jrhahn/rs-birdscale/src/platform.rs

//! Concrete ESP32-C3 wiring for the sensor abstraction (#12).
//!
//! `sensors/` is HAL-agnostic; this module is where it meets the board. It
//! brings up the buses this node actually needs (per [`node::active`]),
//! constructs the enabled drivers, and offers one `measure_all()` that the
//! publish path can call without knowing what is populated.
//!
//! ## Pin map (Seeed XIAO ESP32-C3 silkscreen -> GPIO)
//!
//! | Pad | GPIO | Use |
//! | --- | --- | --- |
//! | D0 | 2  | HX711 SCK |
//! | D1 | 3  | HX711 DT |
//! | D2 | 4  | DS18B20 1-Wire, *or* the battery divider's tap on ADC1 |
//! | D3 | 5  | SDS011 UART RX (sensor TX) |
//! | D4 | 6  | I²C SDA (SHT31-D, SCD41) |
//! | D5 | 7  | I²C SCL |
//! | D10| 10 | SDS011 UART TX (sensor RX) |
//!
//! The SDS011 deliberately avoids D6/D7 (GPIO21/20): those are the console UART
//! pads, and the log output shares them.
//!
//! The two I²C sensors sit on one bus at different addresses (0x44 / 0x62), so
//! the bus is wrapped in a [`SharedI2c`] handle that each driver can own.

use embassy_sync::{blocking_mutex::raw::NoopRawMutex, mutex::Mutex};
use embassy_time::{with_timeout, Duration, TimeoutError};
use embedded_hal_async::i2c::{ErrorType, I2c as I2cTrait, Operation};
use esp_hal::{
    gpio::GpioPin,
    i2c::master::{Config as I2cConfig, Error as I2cError, I2c},
    peripherals::{I2C0, UART1},
    uart::{Config as UartConfig, Uart},
    Async,
};
use heapless::Vec;
use log::{info, warn};
use static_cell::StaticCell;

use crate::node::{self, Slot};
use crate::sensors::{
    scd41, scd41::Scd41, sds011::Sds011, sgp41, sgp41::Sgp41, sht31, sht31::Sht31, Reading, Sensor,
};

/// SDS011 baud rate (fixed in hardware).
const SDS011_BAUD: u32 = 9600;

/// Upper bound on the readings one round can produce: weight + probe
/// temperature + SHT31 (2) + SCD41 (3) + SDS011 (2) + cell voltage + link
/// RSSI, with headroom.
///
/// Kept in step with [`crate::discovery::MAX_ENTITIES`]: a node that announces
/// an entity it then has no room to report would look broken in exactly the
/// way that is hardest to see, because `push_sample` drops silently.
pub const MAX_SAMPLES: usize = 14;

/// One reading plus the node-level key prefix that disambiguates it (see
/// [`Slot`]). The publish path turns this into `<ns>/<node>/<prefix><key>`.
pub struct Sample {
    pub prefix: &'static str,
    pub reading: Reading,
}

/// The set of readings gathered in one round.
pub type Samples = Vec<Sample, MAX_SAMPLES>;

// --- Shared I²C bus ----------------------------------------------------------

type I2cBus = I2c<'static, Async>;
static I2C_BUS: StaticCell<Mutex<NoopRawMutex, I2cBus>> = StaticCell::new();

/// A cloneable handle to the one I²C peripheral, so both I²C drivers can own
/// their bus (as the [`Sensor`] contract wants) while sharing the hardware.
/// `NoopRawMutex` is sufficient: everything runs on the single-core executor and
/// measurements are sequential, the lock only enforces that at compile time.
#[derive(Clone, Copy)]
pub struct SharedI2c(&'static Mutex<NoopRawMutex, I2cBus>);

impl ErrorType for SharedI2c {
    type Error = I2cError;
}

/// Ceiling on one I²C transaction. Nothing on this bus is slow: the longest
/// thing any driver asks for is a handful of bytes at 100 kHz, and the sensors'
/// own conversion waits happen *between* transactions, not inside them. So a
/// transaction still running after this is not slow, it is stuck.
///
/// It exists because the alternative is worse than an error. `transaction` is
/// awaited with no bound of its own, so a bus wedged by a device holding SDA
/// low parks the caller for ever: no reading, no log line, and eventually the
/// system watchdog reboots the node — which is what `rst:0x7 (TG0WDT_SYS_RST)`
/// in the outdoor node's log was. A timeout turns that into a failed reading
/// the drivers already know how to report.
pub const I2C_TIMEOUT_MS: u64 = 100;

impl I2cTrait for SharedI2c {
    async fn transaction(
        &mut self,
        address: u8,
        operations: &mut [Operation<'_>],
    ) -> Result<(), Self::Error> {
        // Spell the trait out: esp-hal's `I2c` also has an inherent
        // `transaction` taking its own `Operation` type, which would shadow this.
        let mut bus = self.0.lock().await;
        match with_timeout(
            Duration::from_millis(I2C_TIMEOUT_MS),
            I2cTrait::transaction(&mut *bus, address, operations),
        )
        .await
        {
            Ok(result) => result,
            Err(TimeoutError) => {
                warn!(
                    "I²C transaction to 0x{address:02X} timed out after {I2C_TIMEOUT_MS} ms;                      treating it as a bus fault rather than waiting for the watchdog"
                );
                Err(I2cError::TimeOut)
            }
        }
    }
}

// --- Peripherals this module may claim ---------------------------------------

/// The peripherals the sensor platform can take over. `main` hands these across
/// wholesale; which of them are actually touched depends on the identity.
pub struct Peripherals {
    pub i2c0: I2C0,
    pub sda: GpioPin<6>,
    pub scl: GpioPin<7>,
    pub uart1: UART1,
    pub uart_rx: GpioPin<5>,
    pub uart_tx: GpioPin<10>,
}

/// The drivers populated on this node. Absent sensors are simply `None`, so the
/// publish path is the same code for every node in the fleet.
pub struct Sensors {
    bus: Option<SharedI2c>,
    sht31: Option<Sht31<SharedI2c>>,
    scd41: Option<Scd41<SharedI2c>>,
    sds011: Option<Sds011<Uart<'static, Async>>>,
    /// Unlike every other driver here this one is not read once a round:
    /// its hotplate only stays comparable while it is sampled at 1 Hz, so
    /// [`Sensors::step_gas`] drives it between rounds and `measure_all`
    /// merely collects whatever index those steps produced.
    sgp41: Option<Sgp41<SharedI2c>>,
    /// Whether the I²C bring-up probe has already run this boot.
    probed: bool,
    /// Consecutive rounds the SCD41 produced nothing, and whether its self test
    /// has already run for this streak (see [`SCD41_SELF_TEST_AFTER`]).
    scd41_empty_rounds: u8,
    scd41_self_tested: bool,
    /// Base rounds elapsed since boot, so a slot with its own slower cadence
    /// knows which of them are its own (see [`Slot::rounds_between`]).
    round: u32,
    /// κ in hundredths, from the live config, handed to the SDS011 with the
    /// humidity just before it measures.
    kappa_centi: u32,
}

/// Empty SCD41 rounds before the driver asks the sensor to test itself.
///
/// Three, because one empty round is normal — periodic mode reports nothing
/// until the first conversion finishes — and two in a row can still be a
/// restart. Three is a fault worth ten seconds of diagnosis.
const SCD41_SELF_TEST_AFTER: u8 = 3;

impl Sensors {
    /// Bring up only the buses this node needs and construct its drivers.
    /// [`node::init`] must have run first — the identity decides what exists.
    pub fn new(p: Peripherals) -> Self {
        let node = node::active();

        let bus = if node.uses_i2c() {
            let i2c = I2c::new(p.i2c0, I2cConfig::default())
                .with_sda(p.sda)
                .with_scl(p.scl)
                .into_async();
            Some(SharedI2c(I2C_BUS.init(Mutex::new(i2c))))
        } else {
            None
        };

        let sht31 = match (bus, node.sht31.enabled) {
            (Some(bus), true) => Some(Sht31::new(bus)),
            _ => None,
        };
        let scd41 = match (bus, node.scd41.enabled) {
            (Some(bus), true) => Some(Scd41::new(bus, node.scd41_mode())),
            _ => None,
        };
        let sgp41 = match (bus, node.sgp41.enabled) {
            (Some(bus), true) => Some(Sgp41::new(bus)),
            _ => None,
        };

        let sds011 = if node.uses_uart() {
            // A UART that fails to configure is a wiring/build mistake, not a
            // runtime condition, so log it and carry on without the sensor.
            match Uart::new_with_config(
                p.uart1,
                UartConfig::default().baudrate(SDS011_BAUD),
                p.uart_rx,
                p.uart_tx,
            ) {
                Ok(uart) => {
                    Some(Sds011::new(uart.into_async()).compensated(node.sds011.compensated))
                }
                Err(e) => {
                    warn!("SDS011 UART init failed: {:?}; sensor disabled", e);
                    None
                }
            }
        } else {
            None
        };

        Self {
            bus,
            sht31,
            scd41,
            sds011,
            sgp41,
            probed: false,
            scd41_empty_rounds: 0,
            scd41_self_tested: false,
            round: 0,
            kappa_centi: crate::sensors::sds011::KAPPA_CENTI_DEFAULT,
        }
    }

    /// Hand the SCD41 its temperature offset (hundredths of °C) from the live
    /// config. A no-op on a node without one, and cheap enough to call every
    /// round — the driver only touches the bus when the value actually changed.
    pub fn set_scd41_offset(&mut self, centi: i32) {
        if let Some(scd41) = self.scd41.as_mut() {
            scd41.set_temperature_offset(centi);
        }
    }

    /// Hand the SDS011 its humidity-correction constant from the live config.
    /// A no-op on a node without one; the humidity itself is picked up inside
    /// [`Sensors::measure_all`], where the SHT31 has just been read.
    pub fn set_sds011_kappa(&mut self, centi: u32) {
        self.kappa_centi = centi;
    }

    /// One 1 Hz step of the gas sensor. A no-op on a node without one.
    ///
    /// This exists because the SGP4x is the one part here that cannot be read
    /// once a round: what it returns is a hotplate resistance, comparable only
    /// while the heater keeps running, and Sensirion's index algorithm is
    /// specified for a 0.5-10 s interval. Sampled once a minute it would yield
    /// a number that looks like a VOC index and is not one -- so the caller
    /// ticks this every second between publishes and `measure_all` only reports
    /// what the ticks computed.
    pub async fn step_gas(&mut self) {
        if let Some(s) = self.sgp41.as_mut() {
            s.sample_once().await;
        }
    }

    /// Whether this node has a gas sensor at all, so the caller can skip the
    /// 1 Hz loop entirely rather than ticking a `None` once a second.
    pub fn has_gas_sensor(&self) -> bool {
        self.sgp41.is_some()
    }

    /// Ask each expected I²C address whether anything is there, and say so in
    /// the log. Without this a wiring fault, a missing pull-up and a strapped
    /// address all look identical from the outside: "not responding".
    ///
    /// The probe commands are side-effect-free reads, and an SHT31-D found only
    /// at the alternate address is adopted rather than reported as missing —
    /// breakouts differ on how they strap ADDR.
    async fn probe_i2c(&mut self) {
        let Some(bus) = self.bus else { return };
        let mut missing = false;

        if self.sht31.is_some() {
            // Ask for a known state before asking anything else. A battery node
            // cold-boots every couple of seconds while the sensor stays powered
            // from 3V3, so a restart can land mid-transaction and leave the
            // SHT31 part-way through a command -- still ACKing its address, so
            // the bus scan finds it, but NAKing what comes next. That is the
            // "0x44 answered" / "no SHT31-D at 0x44" pair in the log.
            if let Some(s) = self.sht31.as_mut() {
                s.soft_reset().await;
            }
            let primary = acks(bus, sht31::ADDR, sht31::CMD_READ_STATUS).await;
            let alt = acks(bus, sht31::ADDR_ALT, sht31::CMD_READ_STATUS).await;
            match (primary, alt) {
                (true, _) => info!("SHT31-D found at 0x{:02X}", sht31::ADDR),
                (false, true) => {
                    info!(
                        "SHT31-D found at 0x{:02X} (ADDR strapped high); using it",
                        sht31::ADDR_ALT
                    );
                    let mut moved = Sht31::with_address(bus, sht31::ADDR_ALT);
                    // The reset above went to the default address, which is not
                    // where this one lives.
                    moved.soft_reset().await;
                    self.sht31 = Some(moved);
                }
                (false, false) => {
                    missing = true;
                    warn!(
                        "no SHT31-D at 0x{:02X} or 0x{:02X}",
                        sht31::ADDR,
                        sht31::ADDR_ALT
                    );
                }
            }
        }

        if self.scd41.is_some() {
            if acks(bus, scd41::ADDR, scd41::CMD_GET_DATA_READY).await {
                info!("SCD41 found at 0x{:02X}", scd41::ADDR);
                // The address ACK only proves something is on the bus. The
                // serial number says *what* — which physical sensor sits in
                // this node, and whether it is plausibly a genuine Sensirion
                // part at all. Counterfeits are common and tend to answer with
                // zeroes or with the same number on every unit.
                if let Some(s) = self.scd41.as_mut() {
                    match s.serial_number().await {
                        Some(0) => warn!(
                            "SCD41 serial number is zero — that is not what a genuine \
                             Sensirion part returns; treat its readings with suspicion"
                        ),
                        Some(serial) => info!("SCD41 serial 0x{:012X}", serial),
                        None => warn!("SCD41 gave no serial number"),
                    }
                }
            } else {
                missing = true;
                warn!("no SCD41 at 0x{:02X}", scd41::ADDR);
            }
        }

        if self.sgp41.is_some() {
            // `detect` is what the sampling path uses anyway, and it answers a
            // question a bare ACK cannot: an SGP40 and an SGP41 share this
            // address, and only one of them has a NOx channel. Breakout
            // listings mix the two up routinely, so the boot log is the place
            // to find out which one is actually fitted.
            if let Some(s) = self.sgp41.as_mut() {
                match s.detect().await {
                    Some(part) => {
                        info!("{:?} found at 0x{:02X}", part, sgp41::ADDR);
                        match s.serial_number().await {
                            Some(serial) => info!("SGP4x serial 0x{:012X}", serial),
                            None => warn!("SGP4x gave no serial number"),
                        }
                    }
                    None => {
                        missing = true;
                        warn!("no SGP4x at 0x{:02X}", sgp41::ADDR);
                    }
                }
            }
        }

        // Only now, and only because something is already wrong: sweep the bus
        // to tell "the bus is dead" from "the bus is fine and the device is
        // somewhere else". Those two look identical from a targeted probe, and
        // they have completely different fixes.
        if missing {
            self.report_scan(bus).await;
        }
    }

    /// Sweep the whole bus and say what that means, in the terms someone
    /// holding a soldering iron can act on.
    async fn report_scan(&self, mut bus: SharedI2c) {
        let found = crate::sensors::scan_bus(&mut bus).await;
        if found.is_empty() {
            warn!(
                "I²C scan: nothing answered between 0x{:02X} and 0x{:02X} — \
                 the bus itself is not working (SDA/SCL swapped, no pull-ups, or no power)",
                crate::sensors::SCAN_FIRST,
                crate::sensors::SCAN_LAST
            );
            return;
        }
        // Something answered, so the wiring and the pull-ups are fine.
        for addr in &found {
            info!("I²C scan: 0x{:02X} answered", addr);
        }
        warn!(
            "I²C scan: the bus works, so the missing sensor is at none of those \
             addresses — check which device is actually fitted and how it straps its address"
        );
    }

    /// Measure every populated sensor and append the readings to `out`.
    ///
    /// A sensor that does not answer contributes nothing and is logged — never
    /// fatal, matching the DS18B20 contract. This is only called on publish
    /// cycles: the SDS011 in particular spends 10–30 s spinning its fan here.
    pub async fn measure_all(&mut self, out: &mut Samples) {
        let node = node::active();

        // Once per boot, ahead of the first reading, so the log says *why* a
        // sensor is quiet before it is quiet. A few I²C transactions; the
        // battery node's cheap idle wakes never get here at all.
        if !self.probed {
            self.probed = true;
            self.probe_i2c().await;
        }

        let round = self.round;
        self.round = self.round.wrapping_add(1);

        // The SHT31 goes first on purpose: a compensated SDS011 further down
        // needs this round's humidity, and reading it here means the correction
        // uses air from the same minute rather than the previous round's.
        let mut humidity = None;
        if let Some(s) = self.sht31.as_mut() {
            if due(round, node.sht31, &node) {
                collect(s, node.sht31, out).await;
                // Only from a round it actually ran: a skipped round would hand
                // over the previous one's figure, and a correction is only
                // worth anything against air measured at the same time.
                humidity = s.last_humidity_tenths();
            }
        }
        if let Some(s) = self.scd41.as_mut() {
            if !due(round, node.scd41, &node) {
                // Nothing to do this round; leave the empty-round streak alone,
                // since a skipped round is not a silent sensor.
            } else if collect(s, node.scd41, out).await {
                self.scd41_empty_rounds = 0;
                self.scd41_self_tested = false;
            } else {
                self.scd41_empty_rounds = self.scd41_empty_rounds.saturating_add(1);
                // Once a streak looks like a real fault rather than the usual
                // warm-up, let the sensor judge itself. Ten seconds, once per
                // streak — cheap next to the alternative, which is guessing at
                // wiring and supplies while the sensor knows the answer.
                if self.scd41_empty_rounds >= SCD41_SELF_TEST_AFTER && !self.scd41_self_tested {
                    self.scd41_self_tested = true;
                    match s.self_test().await {
                        Some(true) => warn!(
                            "SCD41 self test passed — the sensor believes it is healthy, \
                             so look at wiring, supply or placement rather than the part"
                        ),
                        Some(false) => warn!(
                            "SCD41 self test reports a malfunction — the part itself is faulty"
                        ),
                        None => warn!("SCD41 did not answer its self test"),
                    }
                }
            }
        }
        // Compensation before collection, and from this round's air: the
        // hotplate's response depends on ambient temperature and humidity, and
        // the driver holds the last values it was given until the next round.
        // Skipped when the SHT31 said nothing, because the defaults inside the
        // driver are better than a figure from a different hour.
        if let (Some(gas), Some(sht31)) = (self.sgp41.as_mut(), self.sht31.as_ref()) {
            if let (Some(rh), Some(t)) = (
                sht31.last_humidity_tenths(),
                sht31.last_temperature_tenths(),
            ) {
                gas.compensate(rh, t);
            }
        }

        // Whatever the 1 Hz steps have computed. Empty for the first 45 seconds
        // after a boot (the algorithm's blackout) and while the SGP41 runs its
        // conditioning phase, which is a quiet start rather than a fault -- so
        // unlike `collect` there is no warning here.
        if let Some(gas) = self.sgp41.as_ref() {
            let readings = gas.readings();
            if readings.is_empty() {
                if let Some(why) = gas.fault() {
                    warn!("SGP4x {}; skipping its index", why);
                }
            }
            for reading in readings {
                info!(
                    "SGP4x: {}{} = {}",
                    node.sgp41.prefix_for(reading.key),
                    reading.key,
                    reading.value
                );
                push_sample(out, node.sgp41, reading.key, reading.value);
            }
        }

        if let Some(s) = self.sds011.as_mut() {
            if due(round, node.sds011, &node) {
                if node.sds011.compensated && humidity.is_none() {
                    warn!(
                        "no humidity this round; publishing raw PM only —                          the corrected values will expire until the SHT31 answers again"
                    );
                }
                s.set_ambient(humidity, self.kappa_centi);
                collect(s, node.sds011, out).await;
            }
        }
    }
}

/// Whether a slot measures on this base round (see [`Slot::rounds_between`]).
/// Round 0 is every slot's, so the first publish after a boot is complete
/// rather than missing whichever sensors happen to be on a slow cadence.
fn due(round: u32, slot: Slot, node: &node::NodeConfig) -> bool {
    round % slot.rounds_between(node.sample_secs) == 0
}

/// Does a device acknowledge `addr`? `probe_cmd` must be a command with no side
/// effects — we only care whether the address is ACKed, not what comes back.
async fn acks(mut bus: SharedI2c, addr: u8, probe_cmd: u16) -> bool {
    bus.write(addr, &probe_cmd.to_be_bytes()).await.is_ok()
}

/// Run one sensor and fold its readings into the round's samples. Returns
/// whether it produced anything, so a caller can act on a run of empty rounds.
async fn collect<S: Sensor>(sensor: &mut S, slot: Slot, out: &mut Samples) -> bool {
    let readings = sensor.measure().await;
    if readings.is_empty() {
        match sensor.fault() {
            // The driver knows where it fell over. Say that instead: the boot
            // probe only proves the sensor acknowledges its address, so "not
            // responding" is actively misleading once it does.
            Some(why) => warn!("{} {}; skipping its readings", sensor.kind(), why),
            None => warn!("{} not responding; skipping its readings", sensor.kind()),
        }
        return false;
    }
    for reading in readings {
        info!(
            "{}: {}{} = {}",
            sensor.kind(),
            slot.prefix_for(reading.key),
            reading.key,
            reading.value
        );
        if out
            .push(Sample {
                prefix: slot.prefix_for(reading.key),
                reading,
            })
            .is_err()
        {
            warn!("sample buffer full; dropping remaining readings");
            return true;
        }
    }
    true
}

/// Append a reading produced outside the [`Sensor`] trait (the HX711 weight, the
/// DS18B20 temperature and the battery voltage — all of which need `main`'s
/// state or its peripherals).
pub fn push_sample(out: &mut Samples, slot: Slot, key: &'static str, value: heapless::String<16>) {
    let _ = out.push(Sample {
        prefix: slot.prefix_for(key),
        reading: Reading { key, value },
    });
}
